JhottMaster/steering-wheel-game/controller_game/assets/sprites/coin_star.png

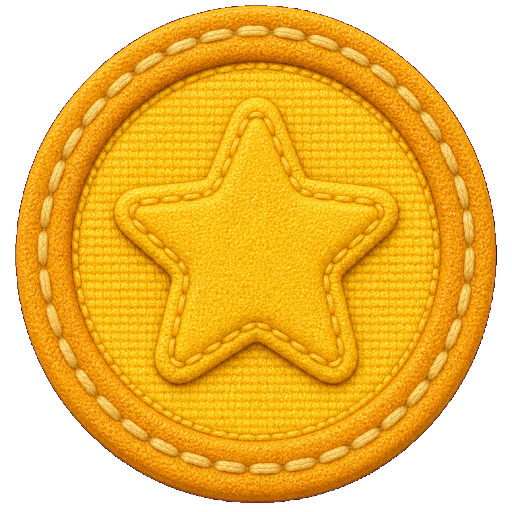
controller_game/assets/sprites/coin_star.png
