JhottMaster/steering-wheel-game/controller_game/assets/sprites/kraken_octopus_road_sheet.png

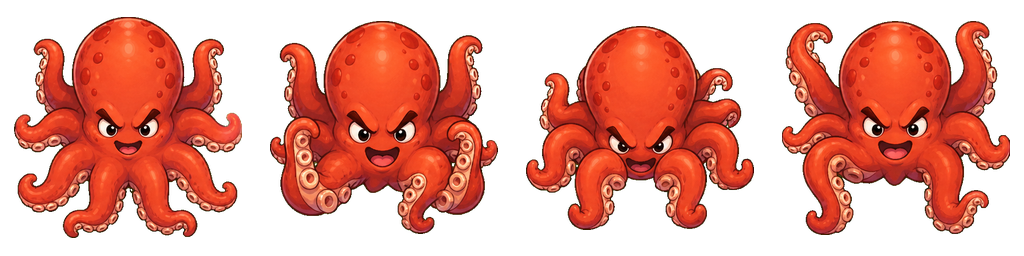
controller_game/assets/sprites/kraken_octopus_road_sheet.png
