JhottMaster/steering-wheel-game/controller_game/assets/sprites/prop_evergreen.png

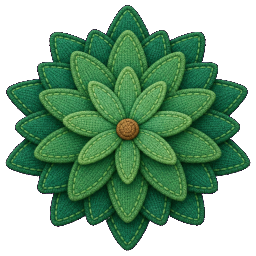
controller_game/assets/sprites/prop_evergreen.png
