JhottMaster/steering-wheel-game/controller_game/assets/sprites/prop_tree_round_ai_01.png

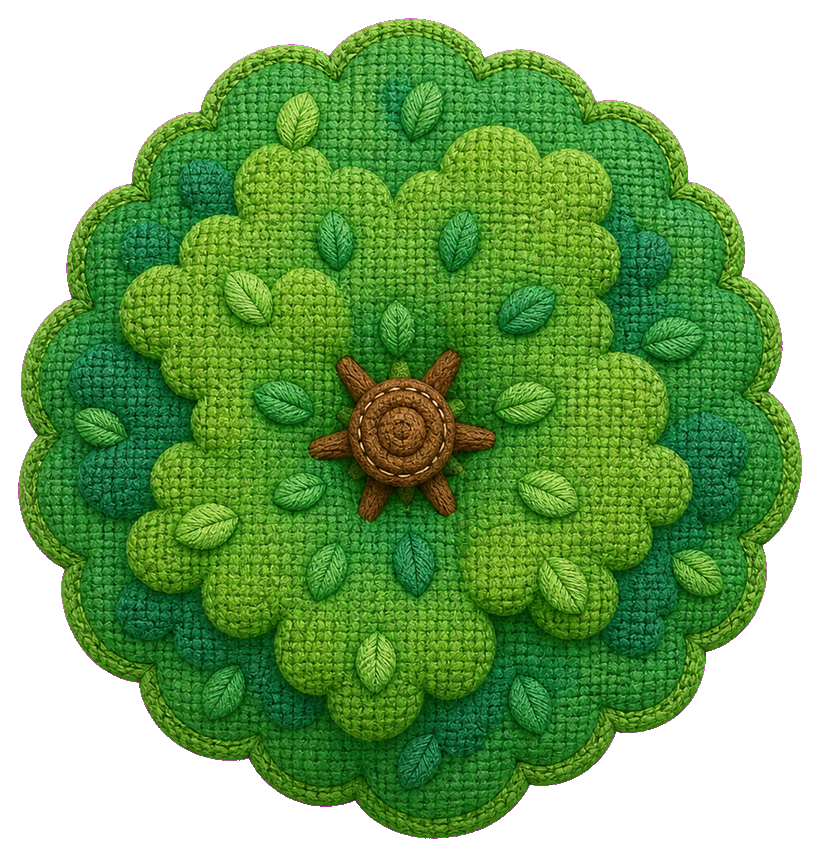
controller_game/assets/sprites/prop_tree_round_ai_01.png
