JhottMaster/steering-wheel-game/controller_game/assets/sprites/road_curve_bottom_left.png

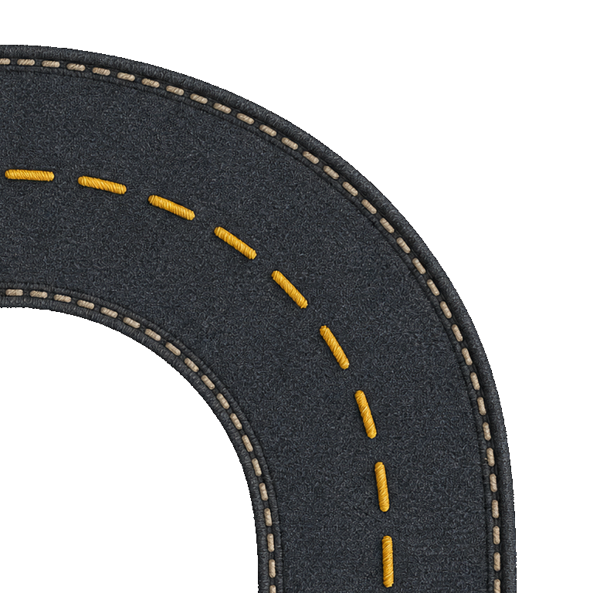
controller_game/assets/sprites/road_curve_bottom_left.png
