JhottMaster/steering-wheel-game/controller_game/assets/sprites/road_curve_top_right.png

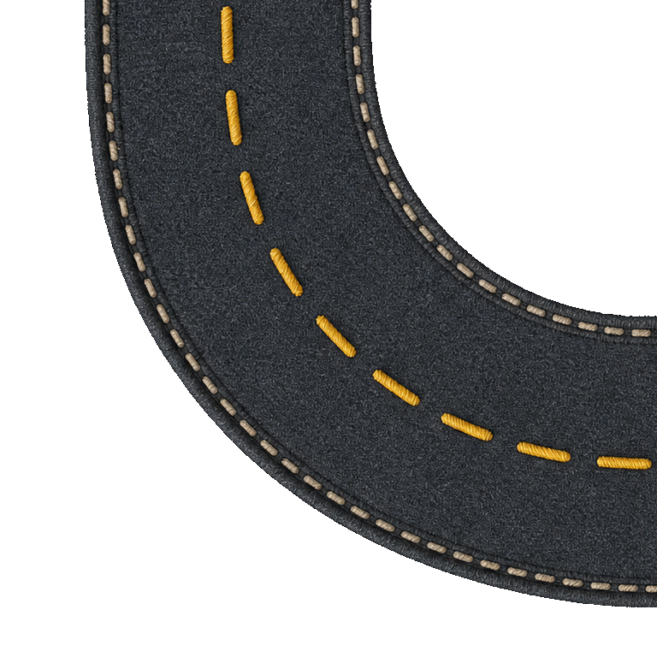
controller_game/assets/sprites/road_curve_top_right.png
