JhottMaster/steering-wheel-game/controller_game/assets/sprites/road_horizontal_repeat.png

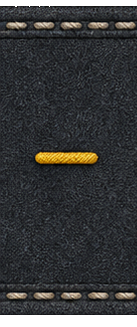
controller_game/assets/sprites/road_horizontal_repeat.png
