JhottMaster/steering-wheel-game/controller_game/assets/sprites/road_intersection_4way_crosswalks.png

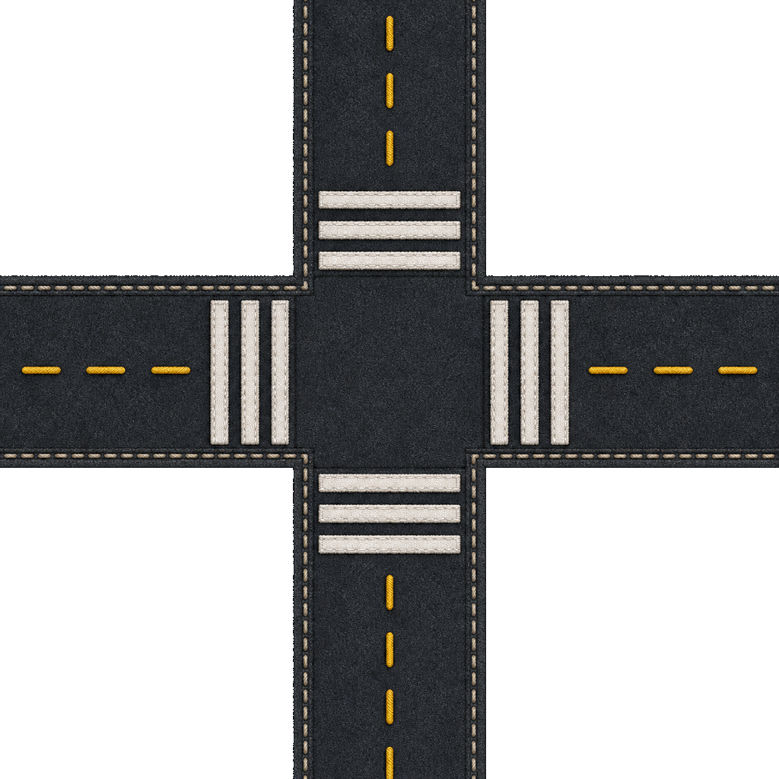
controller_game/assets/sprites/road_intersection_4way_crosswalks.png
