JhottMaster/steering-wheel-game/controller_game/assets/sprites/terrain_carpet_tilemirror.png

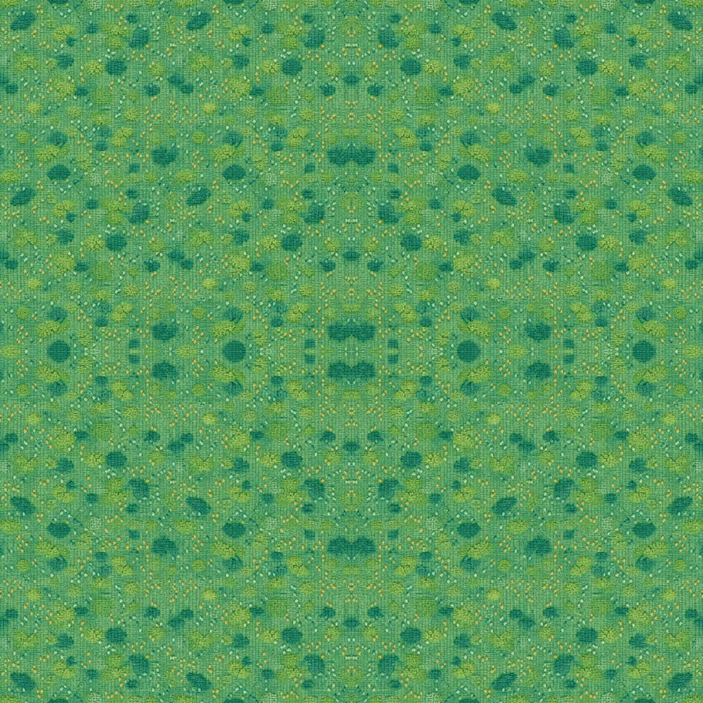
controller_game/assets/sprites/terrain_carpet_tilemirror.png
