JhottMaster/steering-wheel-game/controller_game/assets/sprites/toy_sports_car.png

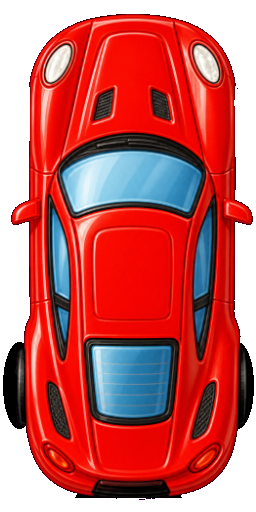
controller_game/assets/sprites/toy_sports_car.png
