JhottMaster/steering-wheel-game/controller_game/assets/sprites/building_daycare.png

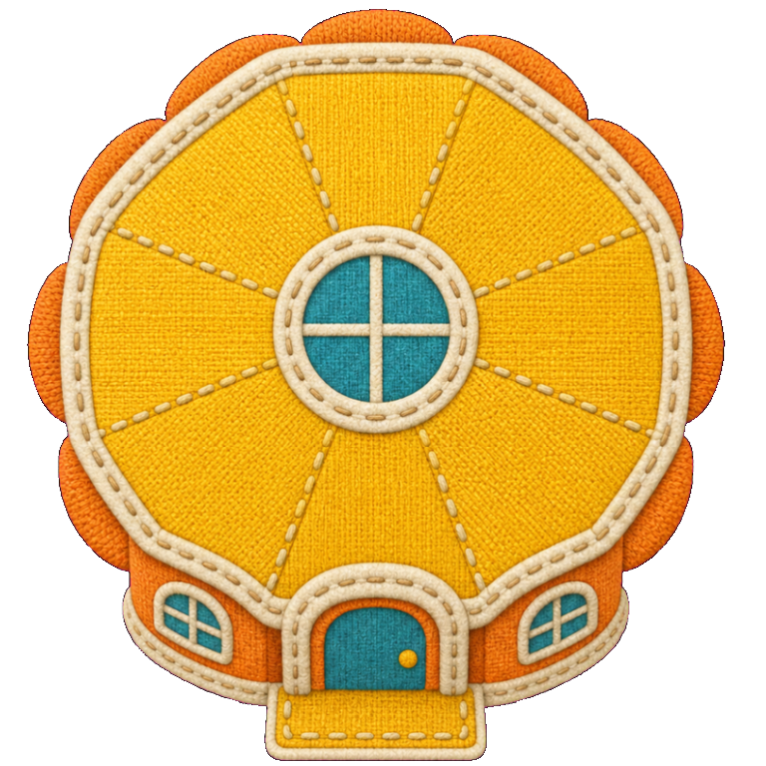
controller_game/assets/sprites/building_daycare.png
