JhottMaster/steering-wheel-game/controller_game/assets/sprites/building_fire_station.png

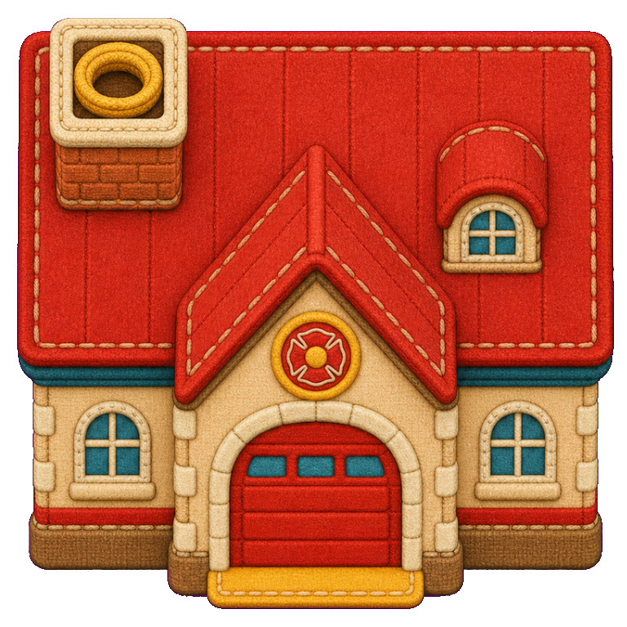
controller_game/assets/sprites/building_fire_station.png
