JhottMaster/steering-wheel-game/controller_game/assets/sprites/building_house.png

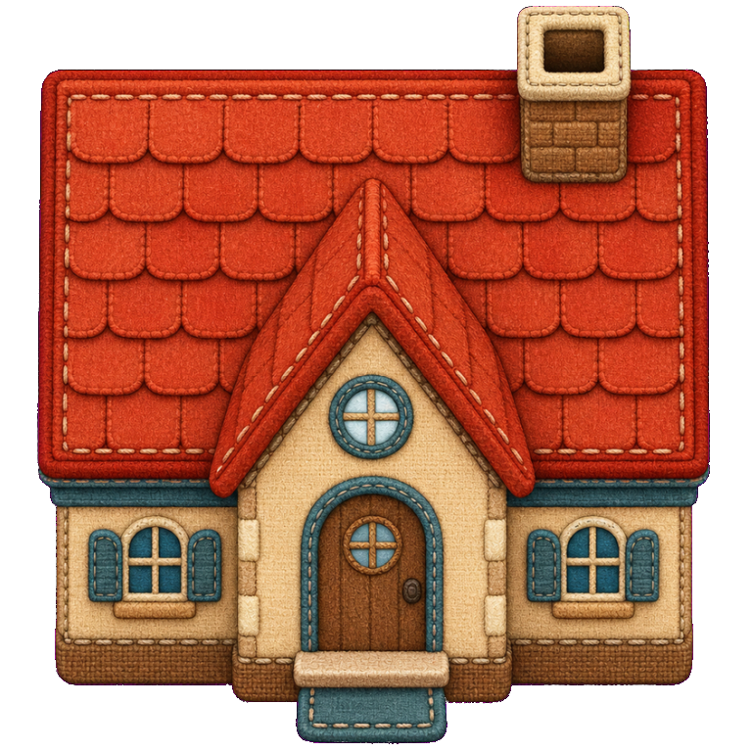
controller_game/assets/sprites/building_house.png
