JhottMaster/steering-wheel-game/controller_game/assets/sprites/building_police_station_ai_01.png

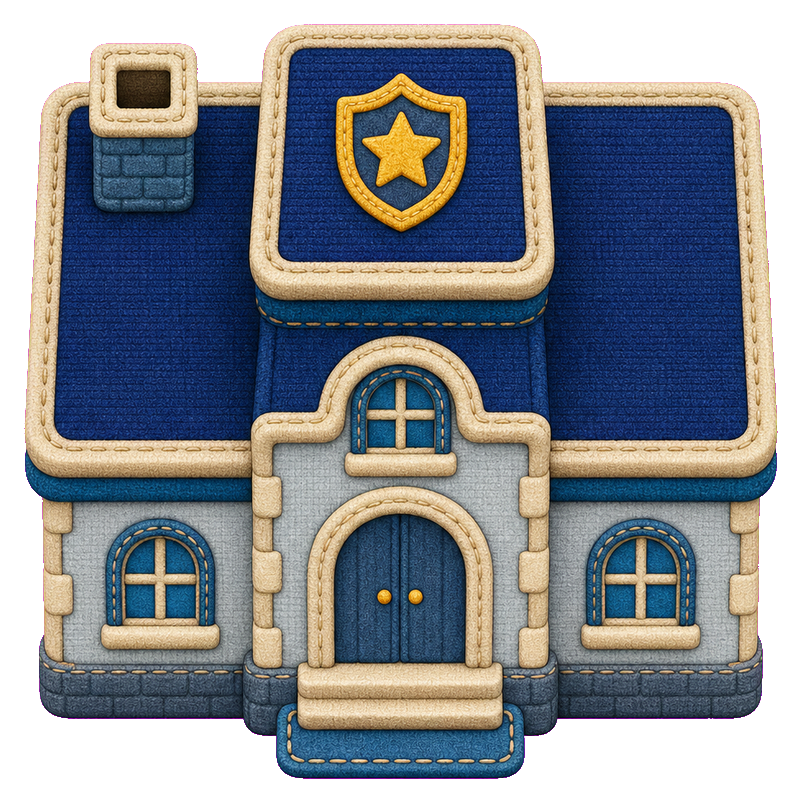
controller_game/assets/sprites/building_police_station_ai_01.png
