JhottMaster/steering-wheel-game/controller_game/assets/sprites/building_shop.png

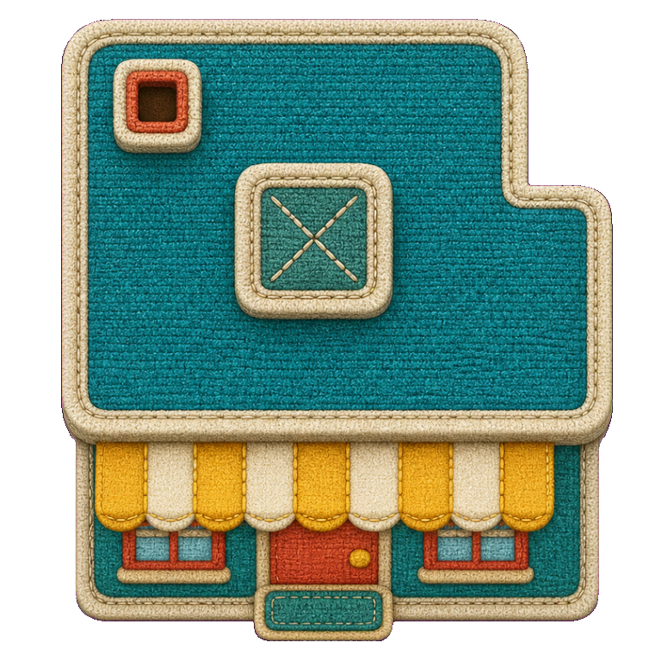
controller_game/assets/sprites/building_shop.png
