JhottMaster/steering-wheel-game/firmware/xiao_bno055_udp_sender/wifi_secrets.example.h

#pragma once

constexpr char kWifiSecretsSsid[] = "REPLACE_WITH_WIFI_SSID";
constexpr char kWifiSecretsPassword[] = "REPLACE_WITH_WIFI_PASSWORD";
// Kept as a manual reference/fallback value while the controller now prefers UDP server discovery.
constexpr char kWifiSecretsHostIp[] = "REPLACE_WITH_HOST_IP";
